azizelse-0v2/macropad/PCB/Pictures/image1.png

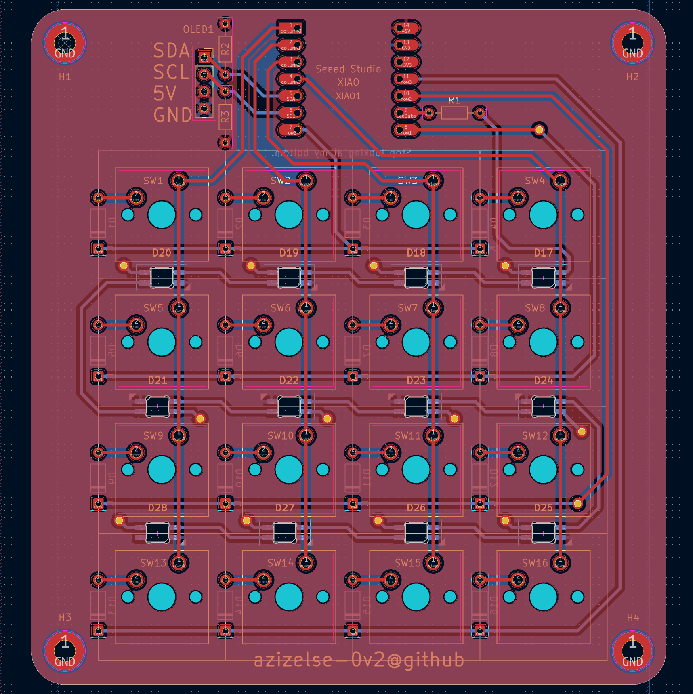
PCB/Pictures/image1.png
