azizelse-0v2/macropad/PCB/Pictures/image3.png

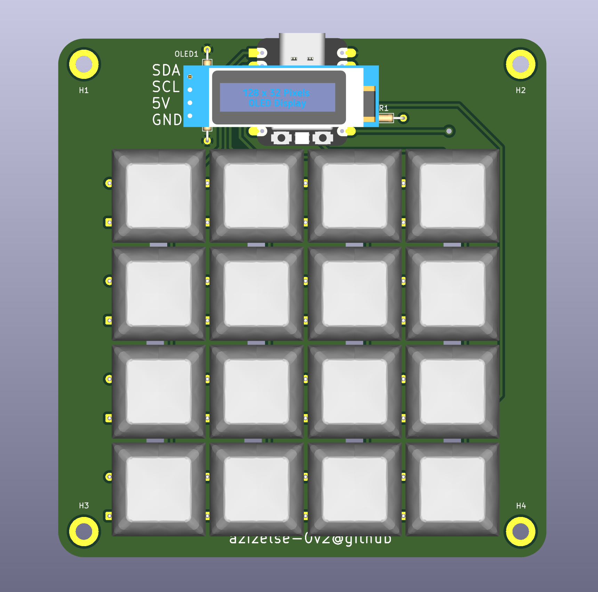
PCB/Pictures/image3.png
