azizelse-0v2/macropad/PCB/Pictures/image4.png

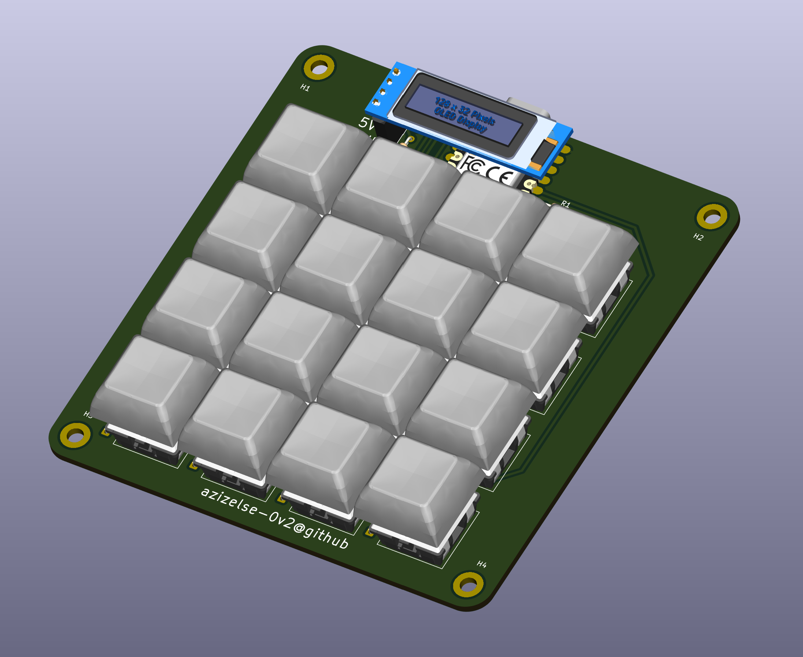
PCB/Pictures/image4.png
