azizelse-0v2/macropad/PCB/Pictures/image5.png

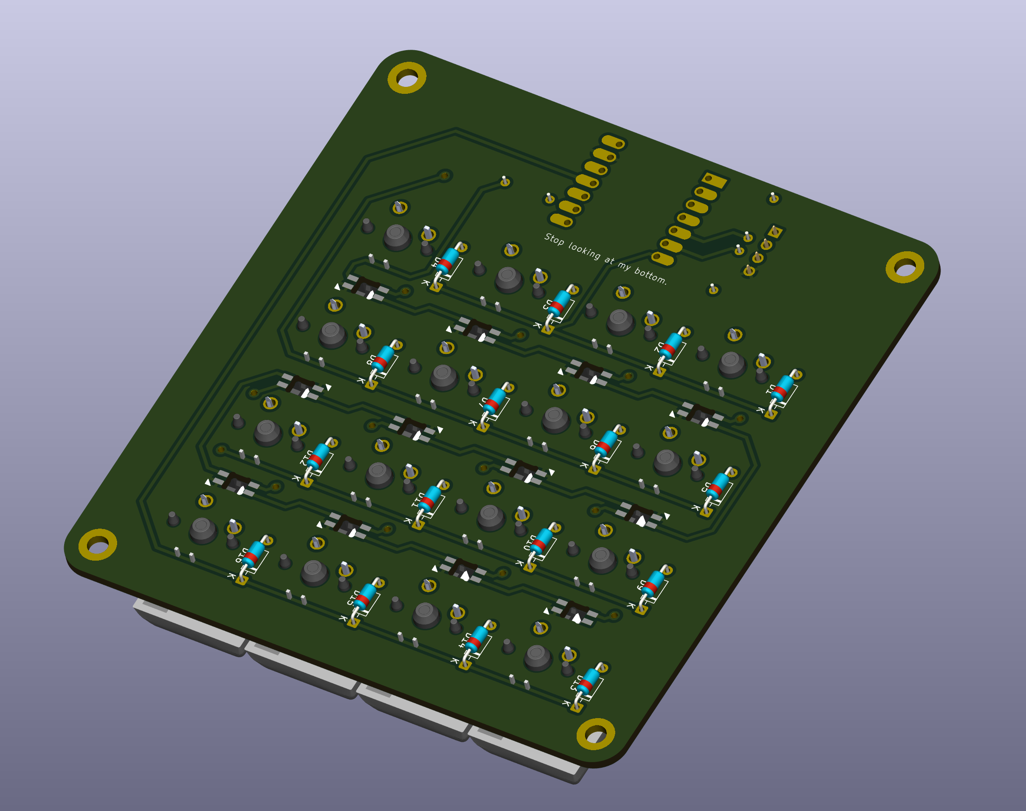
PCB/Pictures/image5.png
